yoavtsur100/Advanced-CPU-architecture-and-Hardware-Accelerators-Lab/Final project - MCU and HW-Accelerators architecture and design/DUT/RV32IMscMCU/CONTROL.VHD

--============================================================================
-- Copyright 2026 Hananya Ribo 
-- Advanced CPU architecture and Hardware Accelerators Lab 361-1-4693 BGU
-- Control-Unit module
--============================================================================ 
LIBRARY IEEE;
USE IEEE.STD_LOGIC_1164.ALL;
USE IEEE.STD_LOGIC_ARITH.ALL;
USE IEEE.STD_LOGIC_SIGNED.ALL;
USE work.const_package.all;


ENTITY control IS
  PORT( 
		--Inputs
		clk_i               : IN    STD_LOGIC; --sync process
		rst_i               : IN    STD_LOGIC; --rst process
		instruction_i 		: IN 	STD_LOGIC_VECTOR(31 DOWNTO 0);
		DIVbusy_i			: In STD_LOGIC;
		--Outputs
		PChold_ctrl_o 		: OUT 	STD_LOGIC;
		RegDst_ctrl_o 		: OUT 	STD_LOGIC;
		ALUSrc_ctrl_o 		: OUT 	STD_LOGIC;
		MemtoReg_ctrl_o 	: OUT 	STD_LOGIC;
		RegWrite_ctrl_o 	: OUT 	STD_LOGIC;
		MemRead_ctrl_o 		: OUT 	STD_LOGIC;
		MemWrite_ctrl_o	 	: OUT 	STD_LOGIC;
		Branch_ctrl_o 		: OUT 	STD_LOGIC;
		Jal_ctrl_o 			: OUT 	STD_LOGIC;
		Jalr_ctrl_o 		: OUT 	STD_LOGIC;
		UpperIm_ctrl_o		: OUT 	STD_LOGIC_VECTOR(1 DOWNTO 0);
		ALUOp_ctrl_o	 	: OUT 	STD_LOGIC_VECTOR(4 DOWNTO 0);
		
		--Multiplier Extension:
		MULop_o  			: OUT STD_LOGIC;
		DIVctrl_o			: OUT STD_LOGIC;
		WBSrc0_o  			: OUT STD_LOGIC;
		WBSrc1_o			: OUT STD_LOGIC_VECTOR(1 DOWNTO 0);
		
		-- Interrupt Extension:
		INTR_i              : IN  STD_LOGIC;
		INTA_o              : OUT STD_LOGIC; --DEFAULT '1'
		ClearGIE_ctrl_o     : OUT STD_LOGIC;
		SetGIE_ctrl_o       : OUT STD_LOGIC;
		WriteTP_ctrl_o      : OUT STD_LOGIC;
		SelectTypeAddr_ctrl_o : OUT STD_LOGIC;
		IntJump_ctrl_o      : OUT STD_LOGIC;
		IntAccept_ctrl_o    : OUT STD_LOGIC
		);
END control;


ARCHITECTURE behavior OF control IS

	TYPE state_type IS (Normal, IntCycle1, IntCycle2); --can be diffrent types for different interupt source
	SIGNAL state_q, next_state_w : state_type := Normal;
	SIGNAL is_reti_w : STD_LOGIC; --for exiting from interrupt

	SIGNAL	Rtype_w, Itype_w, Stype_w, SBtype_w, Utype_w, UJtype_w 								: STD_LOGIC;
	SIGNAL	lb_w, lh_w, lw_w, lbu_w, lhu_w, lwu_w, ld_w, sb_w, sh_w, sw_w, st_w					: STD_LOGIC;
	SIGNAL	beq_w, bne_w, blt_w, bge_w, bltu_w, bgeu_w, branch_w, jal_w, jalr_w 				: STD_LOGIC;
	SIGNAL	add_w, addi_w, and_w, andi_w, or_w, ori_w, sll_w, slli_w, sra_w, srai_w				: STD_LOGIC;
	SIGNAL	srl_w, srli_w, sub_w, xor_w, xori_w, auipc_w, lui_w, slt_w, slti_w, sltu_w, sltiu_w	: STD_LOGIC;
	SIGNAL  opc_w 																				: STD_LOGIC_VECTOR(6 DOWNTO 0);
	--Multiplier+Interrupt Extension:
	SIGNAL mul_w 																				: STD_LOGIC;
	SIGNAL div_w 																				: STD_LOGIC_VECTOR(1 DOWNTO 0);
	signal WBSrc0_w																				: STD_LOGIC;
	signal PChold_ctrl_w																		: STD_LOGIC;
	signal accept_interrupt_w																	: STD_LOGIC;
	signal div_started_q                                                                        : STD_LOGIC := '0';
	signal divbusy_q																			: STD_LOGIC;
BEGIN           
	opc_w 		<=	instruction_i(6 DOWNTO 0);
	-- Code to generate control signals using opcode bits
	Rtype_w		<=  '1'	WHEN	opc_w = RTYPE_OPC  ELSE '0';
	Itype_w		<=  '1'	WHEN	(opc_w = ITYPE_OPC) or (ld_w = '1') or (jalr_w = '1') ELSE '0';
	Stype_w 	<=  '1'	WHEN	opc_w = STYPE_OPC  ELSE '0';
	SBtype_w 	<=  '1'	WHEN	opc_w = SBTYPE_OPC ELSE '0';
	Utype_w 	<=  '1'	WHEN	((opc_w and UTYPE_OPC) = UTYPE_OPC)  ELSE '0';
	UJtype_w 	<=  '1'	WHEN	opc_w = UJTYPE_OPC ELSE '0';

	lb_w		<=	'1'	WHEN	(instruction_i and INST_LB_MASK) = INST_LB				ELSE 	'0';	--lb		
	lh_w		<=	'1'	WHEN	(instruction_i and INST_LH_MASK) = INST_LH				ELSE 	'0';	--lh
	lw_w		<=	'1'	WHEN	(instruction_i and INST_LW_MASK) = INST_LW				ELSE 	'0';	--lw
	lbu_w		<=	'1'	WHEN	(instruction_i and INST_LBU_MASK) = INST_LBU			ELSE	'0';	--lbu
	lhu_w		<=	'1'	WHEN	(instruction_i and INST_LHU_MASK) = INST_LHU			ELSE	'0';	--lhu
	lwu_w		<=	'1'	WHEN	(instruction_i and INST_LWU_MASK) = INST_LWU			ELSE	'0';	--lwu
	
	ld_w 		<=	'1' WHEN 	 lb_w or lh_w or lw_w or lbu_w or lhu_w or lwu_w	ELSE	'0';	--Load      
													
	sb_w		<=	'1'	WHEN	(instruction_i and INST_SB_MASK) = INST_SB				ELSE	'0';	--sb
	sh_w		<=	'1'	WHEN	(instruction_i and INST_SH_MASK) = INST_SH				ELSE	'0';	--sh
	sw_w		<=	'1'	WHEN	(instruction_i and INST_SW_MASK) = INST_SW				ELSE	'0';	--sw																																						               
	
	st_w		<=	'1'	WHEN	sb_w or sh_w or sw_w															ELSE	'0';	--Store   	
													
	beq_w		<=	'1'	WHEN	(instruction_i and INST_BEQ_MASK) = INST_BEQ			ELSE	'0';	--beq												
	bne_w		<=	'1'	WHEN	(instruction_i and INST_BNE_MASK) = INST_BNE			ELSE	'0';	--bne
	blt_w		<=	'1'	WHEN	(instruction_i and INST_BLT_MASK) = INST_BLT			ELSE	'0';	--blt
	bge_w		<=	'1'	WHEN	(instruction_i and INST_BGE_MASK) = INST_BGE			ELSE	'0';	--bge
	bltu_w	<=	'1'	WHEN	(instruction_i and INST_BLTU_MASK) = INST_BLTU		ELSE	'0';	--bltu
	bgeu_w	<=	'1'	WHEN	(instruction_i and INST_BGEU_MASK) = INST_BGEU		ELSE	'0';	--bgeu
	
	branch_w	<=	'1'	WHEN	beq_w or bne_w or blt_w or bge_w or bltu_w or bgeu_w		ELSE	'0';	--Branch     	
																										
	jal_w		<=		'1'	WHEN	(instruction_i and INST_JAL_MASK) = INST_JAL	ELSE 	'0';		--jal	

	jalr_w	<=	'1'	WHEN	(instruction_i and INST_JALR_MASK) = INST_JALR	ELSE 	'0';
	
	add_w		<=	'1' WHEN	(instruction_i and INST_ADD_MASK) = INST_ADD	ELSE	'0';			--add	
	
	addi_w	<=	'1' WHEN	(instruction_i and INST_ADDI_MASK) = INST_ADDI	ELSE	'0';		--addi
	
	auipc_w	<=	'1' WHEN	(instruction_i and INST_AUIPC_MASK) = INST_AUIPC	ELSE	'0';	--auipc
	
	lui_w		<=	'1' WHEN	(instruction_i and INST_LUI_MASK) = INST_LUI	ELSE	'0';			--lui
	
	and_w		<=	'1' WHEN	(instruction_i and INST_AND_MASK) = INST_AND	ELSE	'0';			--and
	
	andi_w	<=	'1' WHEN	(instruction_i and INST_ANDI_MASK) = INST_ANDI	ELSE	'0';		--andi
	
	or_w		<=	'1' WHEN	(instruction_i and INST_OR_MASK) = INST_OR	ELSE	'0';				--or
	
	ori_w		<=	'1' WHEN	(instruction_i and INST_ORI_MASK) = INST_ORI	ELSE	'0';			--ori
	
	sll_w		<=	'1' WHEN	(instruction_i and INST_SLL_MASK) = INST_SLL	ELSE	'0';			--sll
	
	slli_w 	<=	'1' WHEN	(instruction_i and INST_SLLI_MASK) = INST_SLLI	ELSE	'0';		--slli
	
	sra_w 	<=	'1' WHEN	(instruction_i and INST_SRA_MASK) = INST_SRA	ELSE	'0';			-- sra
	
	srai_w 	<=	'1' WHEN	(instruction_i and INST_SRAI_MASK) = INST_SRAI	ELSE	'0';		-- srai
	
	srl_w 	<=	'1' WHEN	(instruction_i and INST_SRL_MASK) = INST_SRL	ELSE	'0';			-- srl
	
	srli_w 	<=	'1' WHEN	(instruction_i and INST_SRLI_MASK) = INST_SRLI	ELSE	'0';		-- srli
	
	sub_w 	<=	'1' WHEN	(instruction_i and INST_SUB_MASK) = INST_SUB	ELSE	'0';			-- sub
	
	xor_w 	<=	'1' WHEN	(instruction_i and INST_XOR_MASK) = INST_XOR	ELSE	'0';			-- xor
	
	xori_w 	<=	'1' WHEN	(instruction_i and INST_XORI_MASK) = INST_XORI	ELSE	'0';		-- xori
	
	slt_w 	<=	'1' WHEN	(instruction_i and INST_SLT_MASK) = INST_SLT	ELSE	'0';			-- slt
	
	slti_w 	<=	'1' WHEN	(instruction_i and INST_SLTI_MASK) = INST_SLTI	ELSE	'0';		-- slti
	
	sltu_w 	<=	'1' WHEN	(instruction_i and INST_SLTU_MASK) = INST_SLTU	ELSE	'0';		-- sltu
	
	sltiu_w <=	'1' WHEN	(instruction_i and INST_SLTIU_MASK) = INST_SLTIU	ELSE	'0';	-- sltiu
	
	--because of Interrupt different assigments:
	
	RegWrite_ctrl_o 	<=  '1' WHEN state_q = IntCycle2 ELSE
	                            '0' WHEN state_q = IntCycle1 ELSE
	                            (Rtype_w or Itype_w or Utype_w or UJtype_w); --priority for interrupts 

	MemtoReg_ctrl_o 	<=  '0' WHEN (state_q = IntCycle1 or state_q = IntCycle2) ELSE ld_w; --priority for interrupts 

	MemWrite_ctrl_o 	<=  '0' WHEN (state_q = IntCycle1 or state_q = IntCycle2) ELSE st_w; --priority for interrupts 

	MemRead_ctrl_o 		<=  '1' WHEN state_q = IntCycle2 ELSE 	--priority for interrupts 
	                            '0' WHEN state_q = IntCycle1 ELSE
	                            ld_w;

	Branch_ctrl_o     <=	'0' WHEN (state_q = IntCycle1 or state_q = IntCycle2) ELSE branch_w;--priority for interrupts 

	Jal_ctrl_o				<=	'0' WHEN (state_q = IntCycle1 or state_q = IntCycle2) ELSE jal_w; --priority for interrupts 

	Jalr_ctrl_o				<=	'0' WHEN (state_q = IntCycle1 or state_q = IntCycle2) ELSE jalr_w;  --priority for interrupts 

	RegDst_ctrl_o			<=	'1' WHEN state_q = IntCycle2 ELSE				--priority for interrupts 
	                            '0' WHEN state_q = IntCycle1 ELSE
	                            (jal_w or jalr_w);

	ALUSrc_ctrl_o  		<=  '0' WHEN (state_q = IntCycle1 or state_q = IntCycle2) ELSE 	--priority for interrupts 
	                            (Itype_w or Stype_w or Utype_w or UJtype_w);
	
	
	--Multiplier/Divider Extensions:
	mul_w   <=	'1' WHEN	(instruction_i and INST_MUL_MASK) = INST_MUL	ELSE	'0';	-- mul 
	-- Disable Multiplier during interrupt cycles 
	MULop_o				<= '0' WHEN (state_q = IntCycle1 or state_q = IntCycle2 or accept_interrupt_w = '1') ELSE mul_w;
	
	WBSrc0_w <= '0' WHEN (div_w /= "11") else '1';
	WBSrc0_o <= WBSrc0_w;

	
	div_w   <=	"01" WHEN	(instruction_i and INST_DIV_MASK) = INST_DIV	ELSE
				"00" when 	(instruction_i and INST_REM_MASK) = INST_REM	else
				"10" when 	(instruction_i and INST_MUL_MASK) = INST_MUL	else
				"11";	-- div
	-- Disable Divider during interrupt cycles  and when division has already started to prevent re-triggering
	DIVctrl_o				<= '0' WHEN (state_q = IntCycle1 or state_q = IntCycle2 or accept_interrupt_w = '1' or div_started_q = '1') ELSE 
	                           '1' when (div_w = "01" or  div_w = "00") else '0';			
	WBSrc1_o <= div_w ;
	
	-- Interrupt accept gating (only allow interrupt to be accepted if CPU is not on division)
	accept_interrupt_w <= '1' WHEN (state_q = Normal AND INTR_i = '1' AND divbusy_q = '0') ELSE '0';

	--WAIT if BUSY or Interrupt cycles:
	PChold_ctrl_w <= '1' WHEN (divbusy_q = '1') OR 								
	                          (accept_interrupt_w = '1') OR
	                          (state_q = IntCycle1) OR
	                          ((div_w = "01" or div_w = "00") and div_started_q = '0') ELSE '0';
	PChold_ctrl_o <= PChold_ctrl_w;     -- pc=0 no wait pc=1 wait

	-- division start  stall on the first cycle of div/rem
	process(clk_i, rst_i)
	begin
		if rst_i = '1' then
			divbusy_q <= '0';
		elsif rising_edge(clk_i) then
			divbusy_q <= DIVbusy_i;
		end if;
	end process;

	process(clk_i, rst_i)
	begin
		if rst_i = '1' then
			div_started_q <= '0';
		elsif rising_edge(clk_i) then
			if (div_w = "01" or div_w = "00") then
				if DIVbusy_i = '1' then
					div_started_q <= '1';
				end if;
			else
				div_started_q <= '0';
			end if;
		end if;
	end process;

	-- Interrupt Handshake protocol & Control Output Signals
	
	INTA_o <= '0' WHEN state_q = IntCycle1 ELSE '1'; 				-- Assert INTA only during IntCycle1 to prevent bus conflict in Normal cycle
	ClearGIE_ctrl_o <= '1' WHEN state_q = IntCycle1 ELSE '0'; 		--INTERRUPT IS PROCESSED ,request zero GIE
	SetGIE_ctrl_o <= is_reti_w; 									--end of interruption for output updates ,request 1 GIE when reti
	WriteTP_ctrl_o <= '1' WHEN state_q = IntCycle2 ELSE '0'; 		--jump back permisson (Enable)
	SelectTypeAddr_ctrl_o <= '1' WHEN state_q = IntCycle2 ELSE '0';	--choose Type as address for IVT
	IntJump_ctrl_o <= '1' WHEN state_q = IntCycle2 ELSE '0';		--Pc jump to ISR address
	IntAccept_ctrl_o <= accept_interrupt_w;							--when CPU started Interrupt.

	--reti is decoded when instruction is JALR x0, 0(x4) TP is register X4 in RISC-V 
	is_reti_w <= '1' WHEN instruction_i(6 downto 0) = "1100111" 
	                 AND instruction_i(14 downto 12) = "000" -- funct3 for JALR
	                 AND instruction_i(11 downto 7) = "00000" 
	                 AND instruction_i(19 downto 15) = "00100" 
	                 AND instruction_i(31 downto 20) = "000000000000" ELSE '0';
					 
	--FSM:
	-- State registers update process
	process(clk_i, rst_i)
	begin
		if rst_i = '1' then
			state_q <= Normal;
		elsif rising_edge(clk_i) then
			state_q <= next_state_w;
		end if;
	end process;

	-- State transition logic
	process(state_q, accept_interrupt_w)
	begin
		case state_q is
			when Normal =>
				if accept_interrupt_w = '1' then
					next_state_w <= IntCycle1;
				else
					next_state_w <= Normal;
				end if;
			when IntCycle1 =>
				next_state_w <= IntCycle2;
			when IntCycle2 =>
				next_state_w <= Normal;
			when others =>
				next_state_w <= Normal;
		end case;
	end process;
	
	---------------------------------------------------------------------------------------
	UpperIm_ctrl_o		<=	"01" WHEN auipc_w ELSE
												"10" WHEN	lui_w		ELSE
												"00";
		  						      		
	ALUOp_ctrl_o		 	<=  ALU_ADD									WHEN	add_w	or addi_w or auipc_w or lui_w or jal_w or jalr_w	or ld_w or st_w ELSE																																																				
												
												ALU_AND									WHEN	and_w or andi_w																ELSE																			
																			
												ALU_OR									WHEN	or_w or ori_w																	ELSE
																										
												ALU_SHIFTL							WHEN	sll_w or	slli_w															ELSE																					
																					
												ALU_SHIFTR_ARITH				WHEN	sra_w or	srai_w															ELSE 																									
																								
												ALU_SHIFTR							WHEN	srl_w or srli_w																ELSE																					
												
												ALU_SUB									WHEN	sub_w																					ELSE	
			
												ALU_XOR									WHEN	xor_w or xori_w																ELSE 	
																																						
												ALU_LESS_THAN_SIGNED		WHEN	slt_w or slti_w 															ELSE
																																																				
												ALU_LESS_THAN_UNSIGNED	WHEN	sltu_w or sltiu_w															ELSE																						
																						
												ALU_BEQ									WHEN	beq_w																					ELSE
												
												ALU_BNE									WHEN	bne_w																					ELSE
												
												ALU_BLT									WHEN	blt_w																					ELSE
												
												ALU_BGE									WHEN	bge_w																					ELSE
												
												ALU_BLTU								WHEN	bltu_w																				ELSE
												
												ALU_BGEU								WHEN	bgeu_w																				ELSE
												
												ALU_NONE;
	

END behavior;
