yoavtsur100/Advanced-CPU-architecture-and-Hardware-Accelerators-Lab/LAB1 - Concurrent HDL design (VHDL part1)/TB/tb_top.vhd

library IEEE;
use ieee.std_logic_1164.all;
use ieee.std_logic_arith.all;
use ieee.std_logic_unsigned.all;
USE work.aux_package.all;
---------------------------------------------------------
entity tb_top is
	constant n : integer := 8;
	constant k : integer := 3;   -- k=log2(n)
	constant m : integer :=4;   -- m=2^(k-1)
	constant ROWmax : integer :=37 ; --  
end tb_top;
------------------------------------------------------------------------------
architecture tptb of tb_top is
	type mem is array (0 to ROWmax) of std_logic_vector(4 downto 0);
	SIGNAL Y,X:  STD_LOGIC_VECTOR (n-1 DOWNTO 0);
	SIGNAL ALUFN :  STD_LOGIC_VECTOR (4 DOWNTO 0);
	SIGNAL ALUout:  STD_LOGIC_VECTOR(n-1 downto 0); -- ALUout[n-1:0]&Cflag
	SIGNAL Nflag,Cflag,Zflag,Vflag: STD_LOGIC; -- Zflag,Cflag,Nflag,Vflag
	SIGNAL Icache : mem := (
							"01000","01001","01010","01011","01100","01000","01001","01111","01101","01000","01011",
							"10000","10001","10010","10000","10001","10010","10111","10101","10000","10001",
							"11001","11010","11101","11110","11011","00100","11000","11111","11010","11001","11011",
							"00000","00001","00010","00011","00100","00111");
begin
	L0 : top generic map (n,k,m) port map(Y,X,ALUFN,ALUout,Nflag,Cflag,Zflag,Vflag);
    
	--------- start of stimulus section ---------------------------------------		
        tb_x_y : process
        begin
		  x <= (others => '1');
		  y <= (others => '1');
		  wait for 50 ns;
		  for i in 0 to 75 loop
			x <= x+5;
			y <= y-2;
			wait for 50 ns;
		  end loop;
		  wait;
        end process;
		 
		
		tb_ALUFN : process
        begin
		  ALUFN <= (others => '0');
		  for i in 0 to ROWmax loop
			ALUFN <= Icache(i);
			wait for 100 ns;
		  end loop;
		  wait;
        end process;
  
end architecture tptb;
