yoavtsur100/Advanced-CPU-architecture-and-Hardware-Accelerators-Lab/Final project - MCU and HW-Accelerators architecture and design/DUT/RV32IMscMCU/EXECUTE.VHD

--============================================================================
-- Copyright 2026 Hananya Ribo 
-- Advanced CPU architecture and Hardware Accelerators Lab 361-1-4693 BGU
-- Execute module (implements the data ALU and Branch Address Adder) 
--============================================================================
LIBRARY IEEE;
USE IEEE.STD_LOGIC_1164.ALL;
USE IEEE.STD_LOGIC_ARITH.ALL;
USE IEEE.STD_LOGIC_SIGNED.ALL;
USE work.const_package.all;
USE work.aux_package.all;

ENTITY  Execute IS
	generic(
		DATA_BUS_WIDTH 	: integer := 32;
		PC_WIDTH 		: integer := 10
	);
	PORT(	
		--Inputs
		clk_i               : IN    STD_LOGIC; -- MCLK
		read_data1_i 		: IN 	STD_LOGIC_VECTOR(DATA_BUS_WIDTH-1 DOWNTO 0);
		read_data2_i 		: IN 	STD_LOGIC_VECTOR(DATA_BUS_WIDTH-1 DOWNTO 0);
		sign_extend_i 		: IN 	STD_LOGIC_VECTOR(DATA_BUS_WIDTH-1 DOWNTO 0);
		UpperIm_ctrl_i		: IN 	STD_LOGIC_VECTOR(1 DOWNTO 0);
		ALUOp_ctrl_i	 	: IN 	STD_LOGIC_VECTOR(4 DOWNTO 0);
		ALUSrc_ctrl_i 		: IN 	STD_LOGIC;
		pc_i				: IN 	STD_LOGIC_VECTOR(PC_WIDTH-1 DOWNTO 0);
		
		--Multiplier Extension:
		divclk_i		: IN 	STD_LOGIC;	-- ACCCLK
		MULop_i 		: IN 	STD_LOGIC;
		Div_ctrl_i		: IN 	STD_LOGIC;
		WBSrc0_i 		: IN 	STD_LOGIC;
		WBSrc1_i		: IN 	STD_LOGIC_VECTOR(1 DOWNTO 0);
		rst_i			: IN 	STD_LOGIC;	
		--Outputs
		brTaken_o 		: OUT	STD_LOGIC;
		alu_res_o 		: OUT	STD_LOGIC_VECTOR(DATA_BUS_WIDTH-1 DOWNTO 0);
		addr_gen_o 		: OUT	STD_LOGIC_VECTOR(PC_WIDTH-1 DOWNTO 0);
		Divbusy_o		: OUT	STD_LOGIC
	);
END Execute;


ARCHITECTURE struct OF Execute IS
	SIGNAL 	ain_w 				: STD_LOGIC_VECTOR(DATA_BUS_WIDTH-1 DOWNTO 0);
	SIGNAL 	bin_w 				: STD_LOGIC_VECTOR(DATA_BUS_WIDTH-1 DOWNTO 0);
	SIGNAL 	sub_res_w 			: STD_LOGIC_VECTOR(DATA_BUS_WIDTH-1 DOWNTO 0);
	SIGNAL 	ltu_res_w 			: STD_LOGIC;
	SIGNAL 	eq_res_w			: STD_LOGIC;
	SIGNAL	msbneq_res_w		: STD_LOGIC;
	SIGNAL	alu_res_r 			: STD_LOGIC_VECTOR(DATA_BUS_WIDTH-1 DOWNTO 0);
	SIGNAL	brTaken_w 			: STD_LOGIC;
	
	SIGNAL	brl_shl_s1_r		: STD_LOGIC_VECTOR(DATA_BUS_WIDTH-1 DOWNTO 0);
	SIGNAL	brl_shl_s2_r		: STD_LOGIC_VECTOR(DATA_BUS_WIDTH-1 DOWNTO 0);
	SIGNAL	brl_shl_s3_r		: STD_LOGIC_VECTOR(DATA_BUS_WIDTH-1 DOWNTO 0);
	SIGNAL	brl_shl_s4_r		: STD_LOGIC_VECTOR(DATA_BUS_WIDTH-1 DOWNTO 0);
	
	SIGNAL	brl_shr_s1_r		: STD_LOGIC_VECTOR(DATA_BUS_WIDTH-1 DOWNTO 0);
	SIGNAL	brl_shr_s2_r		: STD_LOGIC_VECTOR(DATA_BUS_WIDTH-1 DOWNTO 0);
	SIGNAL	brl_shr_s3_r		: STD_LOGIC_VECTOR(DATA_BUS_WIDTH-1 DOWNTO 0);
	SIGNAL	brl_shr_s4_r		: STD_LOGIC_VECTOR(DATA_BUS_WIDTH-1 DOWNTO 0);
	SIGNAL	brl_shr_pad_r		: STD_LOGIC_VECTOR(DATA_BUS_WIDTH-1 DOWNTO 0);
	
	--Multiplier Extension:
	signal resmul_w 			: STD_LOGIC_VECTOR(DATA_BUS_WIDTH-1 DOWNTO 0);
	signal RESIDUE_w,QUOTIENT_w : STD_LOGIC_VECTOR(DATA_BUS_WIDTH-1 DOWNTO 0);
	
	-- Registers to capture divider results in mclk
	signal residue_mclk_reg, quotient_mclk_reg 	: STD_LOGIC_VECTOR(DATA_BUS_WIDTH-1 DOWNTO 0);
	signal AoutSync_w , BoutSync_w 				: STD_LOGIC_VECTOR(DATA_BUS_WIDTH-1 DOWNTO 0);
	signal MULorDIV_w							: STD_LOGIC_VECTOR(DATA_BUS_WIDTH-1 DOWNTO 0);
	signal Div_ctrl_q1 							: std_logic;
	signal Div_ctrl_q2						    : std_logic;
	signal Div_ctrl_q3 							: std_logic;
		
BEGIN
--------------------------------------------------------------------------------------------------------
-- Branch Address Adder
-- addr_gen_o = pc_i + (sign_extend_i << 2)
--------------------------------------------------------------------------------------------------------					  
addr_gen_o	<= pc_i(PC_WIDTH-1 DOWNTO 0) + (sign_extend_i(PC_WIDTH-3 DOWNTO 0) & '0');

--------------------------------------------------------------------------------------------------------
--ALU
--------------------------------------------------------------------------------------------------------
WITH UpperIm_ctrl_i SELECT
	ain_w <= 	read_data1_i																					WHEN	"00",
						((DATA_BUS_WIDTH-PC_WIDTH-1) DOWNTO 0 => '0') & pc_i	WHEN	"01",
						(others => '0')	WHEN	OTHERS;
	
bin_w <= 	read_data2_i	WHEN not ALUSrc_ctrl_i ELSE	sign_extend_i(DATA_BUS_WIDTH-1 DOWNTO 0);


--Reused resuls 
sub_res_w			<= ain_w - bin_w;
ltu_res_w			<= '1' WHEN ain_w < bin_w 					ELSE '0';
eq_res_w			<= '1' WHEN ain_w = bin_w 					ELSE '0'; 
msbneq_res_w	<= '1' WHEN ain_w(31) /= bin_w(31) 	ELSE '0';

--Multiplier Extension:
--Sync DIVENA: CDC avoid Metastability
process(divclk_i, rst_i)
begin
    if rst_i = '1' then
        Div_ctrl_q1 <= '0';
        Div_ctrl_q2 <= '0';
        Div_ctrl_q3 <= '0';
    elsif rising_edge(divclk_i) then
        Div_ctrl_q1 <= Div_ctrl_i;
        Div_ctrl_q2 <= Div_ctrl_q1;
        Div_ctrl_q3 <= Div_ctrl_q2;
    end if;
end process;


MUL: multiplier_16bit port map (rs1_i =>bin_w(15 downto 0) , rs2_i =>ain_w(15 downto 0), mulOP_i=>MULop_i , rd_o=>resmul_w);	

DIV: Divider_32bit    generic map (N => DATA_BUS_WIDTH) port map (DIVCLK_i => divclk_i , DIVRST_i =>rst_i ,DIVENA_i =>Div_ctrl_q3,
																DIVIDEND_i =>AoutSync_w,DIVISOR_i=> BoutSync_w	,DIVBUSY_o =>Divbusy_o,
																QUOTIENT_o =>QUOTIENT_w ,RESIDUE_o =>RESIDUE_w);
Sync1: Sync 			generic map (DATA_BUS_WIDTH => DATA_BUS_WIDTH) port map ( Ain_i=> ain_w, Bin_i=>bin_w ,divclk_i =>divclk_i, DIVRST_i=>rst_i , Ain_o=>AoutSync_w , Bin_o=>BoutSync_w );			

    -- Clocked process to register divider outputs avoid negative Slack
    process(clk_i, rst_i)
    begin
        if rst_i = '1' then
            residue_mclk_reg  <= (others => '0');
            quotient_mclk_reg <= (others => '0');
        elsif rising_edge(clk_i) then
            residue_mclk_reg  <= RESIDUE_w;
            quotient_mclk_reg <= QUOTIENT_w;
        end if;
    end process;

PROCESS (all)
BEGIN
	-- default values
	alu_res_r 		<= (others => '0');
	brTaken_w 		<= '0';
	brl_shl_s1_r	<= (others => '0');
	brl_shl_s2_r	<= (others => '0');
	brl_shl_s3_r	<= (others => '0'); 
	brl_shl_s4_r	<= (others => '0');
	brl_shr_s1_r	<= (others => '0');
	brl_shr_s2_r	<= (others => '0');
	brl_shr_s3_r	<= (others => '0'); 
	brl_shr_s4_r	<= (others => '0');
	brl_shr_pad_r	<= (others => '0');
	
	
 	CASE ALUOp_ctrl_i IS	-- Select ALU operation
		------------------------------------------------------
    -- Arithmetic
    ------------------------------------------------------
		-- add, addi, auipc, jal, jalr
		WHEN ALU_ADD 	=>
			alu_res_r	<= ain_w + bin_w;
			brTaken_w	<= '0';
		
		-- sub
		WHEN ALU_SUB	=>
			alu_res_r	<= sub_res_w;		 
			brTaken_w	<= '0';
		------------------------------------------------------
    -- Logic
    ------------------------------------------------------
		-- and, andi	
    WHEN	ALU_AND 	=>
			alu_res_r	<= ain_w and bin_w;
			brTaken_w	<= '0';
		
		-- or, ori		
	 	WHEN ALU_OR	=>
			alu_res_r	<= ain_w or bin_w;
			brTaken_w	<= '0';
		
		-- xor, xori
		WHEN ALU_XOR 	=>
			alu_res_r	<= ain_w xor bin_w;
			brTaken_w	<= '0';
				
		------------------------------------------------------
    -- Shift Left
    ------------------------------------------------------
		-- sll, slli
 	 	WHEN ALU_SHIFTL	=>
			-- Barrel-Shifter SHL stage 0
			if (bin_w(0) = '1') then
				brl_shl_s1_r <= (ain_w(30 DOWNTO 0) & '0');
			else
				brl_shl_s1_r <= ain_w;
			end if;
					
			-- Barrel-Shifter SHL stage 1
			if (bin_w(1) = '1') then
				brl_shl_s2_r <= (brl_shl_s1_r(29 DOWNTO 0) & "00");
			else
				brl_shl_s2_r <= brl_shl_s1_r;
			end if;
					
			-- Barrel-Shifter SHL stage 2
			if (bin_w(2) = '1')	then
				brl_shl_s3_r <= (brl_shl_s2_r(27 DOWNTO 0) & "0000");
			else
				brl_shl_s3_r <= brl_shl_s2_r;
			end if;
					
			-- Barrel-Shifter SHL stage 3
			if (bin_w(3) = '1')	then
				brl_shl_s4_r <= (brl_shl_s3_r(23 DOWNTO 0) & "00000000");
			else
				brl_shl_s4_r <= brl_shl_s3_r;
			end if;
					
			-- Barrel-Shifter SHL stage 4
			if (bin_w(4) = '1')	then
				alu_res_r <= (brl_shl_s4_r(15 DOWNTO 0) & "0000000000000000");
			else
				alu_res_r <= brl_shl_s4_r;
			end if;
				      
			brTaken_w	<= '0';
		------------------------------------------------------
    -- Shift Right
    ------------------------------------------------------		
		-- srl, srli, sra, srai	
 	 	WHEN ALU_SHIFTR | ALU_SHIFTR_ARITH 	=>
			--if sra? pad with 1's else pad with 0's 
			if (ain_w(31) = '1' and (ALUOp_ctrl_i = ALU_SHIFTR_ARITH)) then
				brl_shr_pad_r <= 32x"FFFF";
			else
				brl_shr_pad_r <= 32x"0000";
			end if;
			
			-- Barrel-Shifter SHR stage 0
			if (bin_w(0) = '1') then
				brl_shr_s1_r <= (brl_shr_pad_r(31) & ain_w(31 DOWNTO 1));
			else
				brl_shr_s1_r <= ain_w;
			end if;
			
			-- Barrel-Shifter SHR stage 1
			if (bin_w(1) = '1') then
				brl_shr_s2_r <= (brl_shr_pad_r(31 DOWNTO 30) & brl_shr_s1_r(31 DOWNTO 2));
			else
				brl_shr_s2_r <= brl_shr_s1_r;
			end if;
			
			-- Barrel-Shifter SHR stage 2
			if (bin_w(2) = '1') then
				brl_shr_s3_r <= (brl_shr_pad_r(31 DOWNTO 28) & brl_shr_s2_r(31 DOWNTO 4));
			else
				brl_shr_s3_r <= brl_shr_s2_r;
			end if;
			
			-- Barrel-Shifter SHR stage 3
			if (bin_w(3) = '1') then
				brl_shr_s4_r <= (brl_shr_pad_r(31 DOWNTO 24) & brl_shr_s3_r(31 DOWNTO 8));
			else
				brl_shr_s4_r <= brl_shr_s3_r;
			end if;
			
			-- Barrel-Shifter SHR stage 4
			if (bin_w(4) = '1')	then
				alu_res_r <= (brl_shr_pad_r(31 DOWNTO 16) & brl_shr_s4_r(31 DOWNTO 16));
			else
				alu_res_r <= brl_shr_s4_r;
			end if;
				   
			brTaken_w	<= '0';		 	 				
		------------------------------------------------------
    -- Comparision
    ------------------------------------------------------
		-- slt, slti
		WHEN ALU_LESS_THAN_SIGNED	=>
			brTaken_w	<= '0';
			IF msbneq_res_w THEN
				IF ain_w(31) THEN
					alu_res_r	<= (0 => '1', others => '0');	--32'h1
				ELSE
					alu_res_r	<= (others => '0');						--32'h0
				END IF;
			ELSE
				IF sub_res_w(31) THEN
					alu_res_r	<= (0 => '1', others => '0');	--32'h1	
				ELSE
					alu_res_r	<= (others => '0');						--32'h0
				END IF;
			END IF;
		
		-- sltu, sltiu 
		WHEN ALU_LESS_THAN_UNSIGNED	=>
			brTaken_w	<= '0';
			IF ltu_res_w THEN
				alu_res_r	<= (0 => '1', others => '0');		--32'h1
			ELSE
				alu_res_r	<= (others => '0');							--32'h0
			END IF;

		------------------------------------------------------
    -- Condional Branch 
    ------------------------------------------------------
		-- beq
		WHEN ALU_BEQ	=>
			alu_res_r	<= (others => '0');
			brTaken_w	<= eq_res_w;
		
		-- bne
		WHEN ALU_BNE	=>
			alu_res_r	<= (others => '0');
			brTaken_w	<= not eq_res_w;
		
		-- blt
		WHEN ALU_BLT	=>
			alu_res_r	<= (others => '0');
			IF msbneq_res_w THEN
				brTaken_w	<= ain_w(31);
			ELSE
				brTaken_w	<= sub_res_w(31);
			END IF;
		
		-- bge
		WHEN ALU_BGE	=>
			alu_res_r	<= (others => '0');
			IF msbneq_res_w THEN
				brTaken_w	<= bin_w(31);
			ELSE
				brTaken_w	<= not sub_res_w(31);
			END IF;
		
		-- bltu
		WHEN ALU_BLTU	=>
			alu_res_r	<= (others => '0');
			brTaken_w	<= ltu_res_w;
		
		-- bgeu
		WHEN ALU_BGEU	=>
			alu_res_r	<= (others => '0');
			brTaken_w	<= not ltu_res_w;
		
 	 	WHEN OTHERS	=>
			alu_res_r	<= (others => '0');
			brTaken_w	<= '0';
			
  END CASE;
		
END PROCESS;
	
--------------------------------------------------------------------------------------------------------
--Multiplier Extension:
	--Mux between MUL and DIV:
	with WBSrc1_i SELECT
		MULorDIV_w <= residue_mclk_reg when "00",
					  quotient_mclk_reg  when "01",
					  resmul_w    when "10",
						(others => '0') when others;

	--Mux between mul and Alu:
	with WBSrc0_i select
	alu_res_o <= MULorDIV_w when '0',
				alu_res_r when OTHERS;
				
	
brTaken_o	<= brTaken_w;
 
END struct;
