yoavtsur100/Advanced-CPU-architecture-and-Hardware-Accelerators-Lab/Final project - MCU and HW-Accelerators architecture and design/DUT/RV32IMscMCU/DMEMORY.VHD

---------------------------------------------------------------------------------------------
-- Copyright 2025 Hananya Ribo 
-- Advanced CPU architecture and Hardware Accelerators Lab 361-1-4693 BGU
---------------------------------------------------------------------------------------------
--  Dmemory module (implements the data memory for the MIPS computer)
LIBRARY IEEE;
USE IEEE.STD_LOGIC_1164.ALL;
USE IEEE.STD_LOGIC_ARITH.ALL;
USE IEEE.STD_LOGIC_SIGNED.ALL;

LIBRARY altera_mf;
USE altera_mf.altera_mf_components.all;

ENTITY dmemory IS
	generic(
		DATA_BUS_WIDTH 	: integer := 32;
		DTCM_ADDR_WIDTH : integer := 8;
		WORDS_NUM 			: integer := 256
	);
	PORT(	
		--Inputs
		clk_i						: IN 	STD_LOGIC;
		rst_i						: IN 	STD_LOGIC;
		dtcm_addr_i 		: IN 	STD_LOGIC_VECTOR(DTCM_ADDR_WIDTH-1 DOWNTO 0);
		dtcm_data_wr_i 	: IN 	STD_LOGIC_VECTOR(DATA_BUS_WIDTH-1 DOWNTO 0);
		MemRead_ctrl_i  : IN 	STD_LOGIC;
		MemWrite_ctrl_i : IN 	STD_LOGIC;
		
		--Outputs
		dtcm_data_rd_o 	: OUT STD_LOGIC_VECTOR(DATA_BUS_WIDTH-1 DOWNTO 0)
	);
END dmemory;



ARCHITECTURE behavior OF dmemory IS
	SIGNAL wrclk_w : STD_LOGIC;
	
BEGIN
	data_memory : altsyncram
	GENERIC MAP  (
		operation_mode			=> "SINGLE_PORT",
		width_a					=> DATA_BUS_WIDTH,
		widthad_a				=> DTCM_ADDR_WIDTH,
		numwords_a 				=> WORDS_NUM,
		lpm_hint 				=> "ENABLE_RUNTIME_MOD = YES,INSTANCE_NAME = DTCM",
		lpm_type 				=> "altsyncram",
		outdata_reg_a 			=> "UNREGISTERED",
		init_file 				=> "C:\Users\yoavt\ModelSim\FinalProject\Benchmark Apps\test\DTCM.hex",
		intended_device_family 	=> "Cyclone"
	)
	PORT MAP (
		wren_a 					=> MemWrite_ctrl_i,
		clock0					=> wrclk_w,
		address_a				=> dtcm_addr_i,
		data_a					=> dtcm_data_wr_i,
		q_a						=> dtcm_data_rd_o	
	);

	wrclk_w <= NOT clk_i;	-- Load memory address register with write clock
	
END behavior;
